josh-lambda/fencing-tester/CAD/Display.SLDPRT

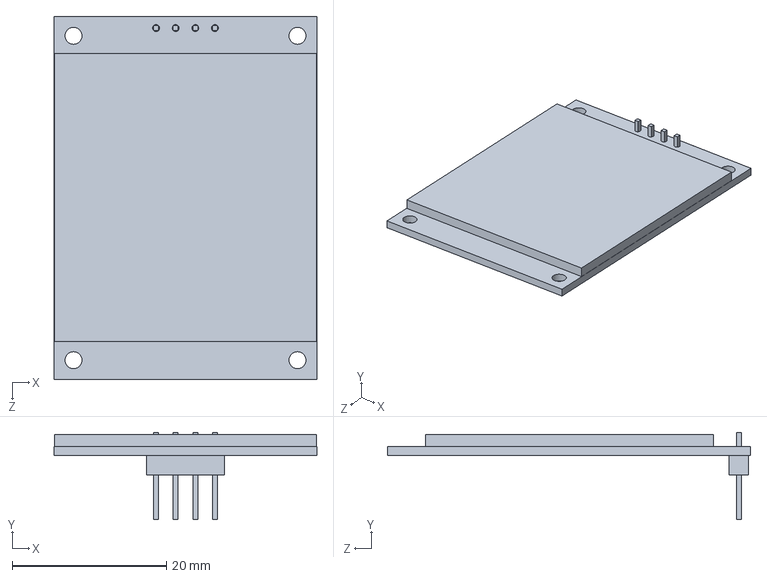
[picture p11: CAD file, 2025-07-18]
CAD/Display.SLDPRT
34.0 x 11.3 x 47.0 mm
